jesionaj/RTOSBot/python/img/orig/Background.png

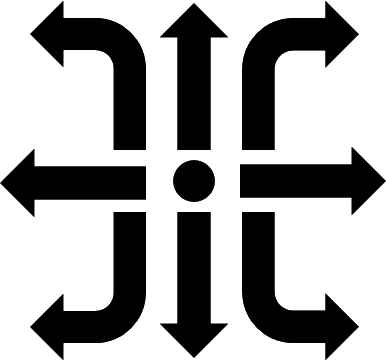
python/img/orig/Background.png
